280Zo/charybdis-wireless-mini-3x6-build-guide/images/pcbs/nice!nano_v2_holder-back.png

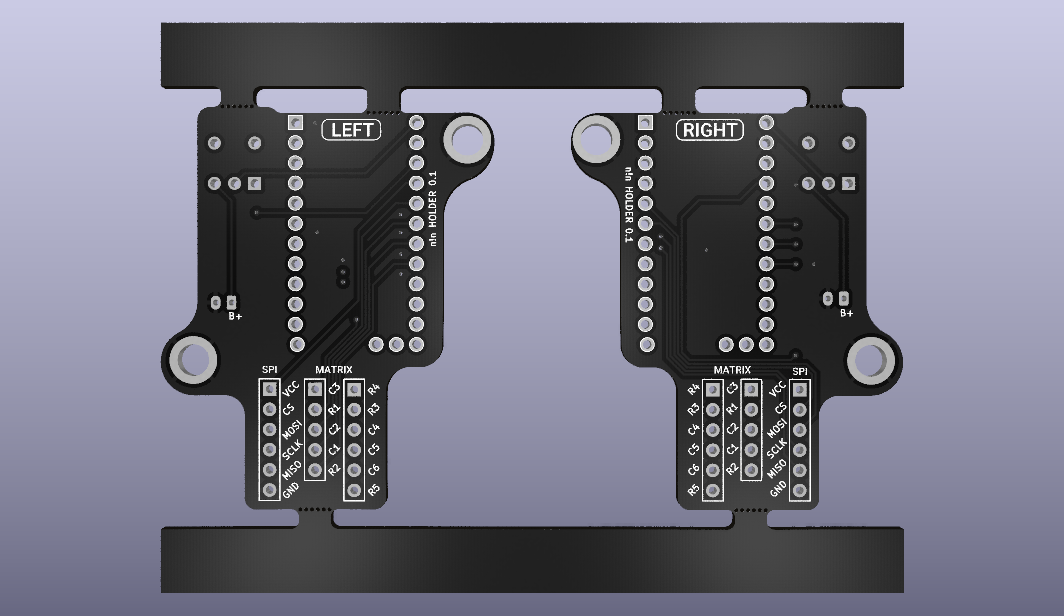
images/pcbs/nice!nano_v2_holder-back.png
