280Zo/charybdis-wireless-mini-3x6-build-guide/3d-print/trackball-parts/trackball-housing-top.stl

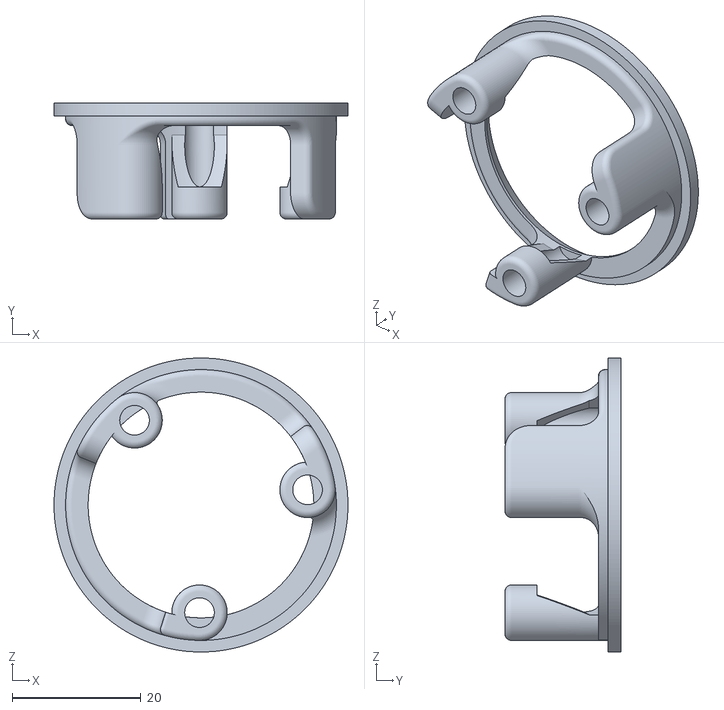
[picture p28: CAD file, 2026-04-28]
3d-print/trackball-parts/trackball-housing-top.stl
45.6 x 18.0 x 45.6
